homelith/pico_sign_sipf_xmodem/pcb/breadboard/breadboard.kicad_sch

## KiCad design pcb/breadboard/breadboard.kicad_sch (2022-04-09)

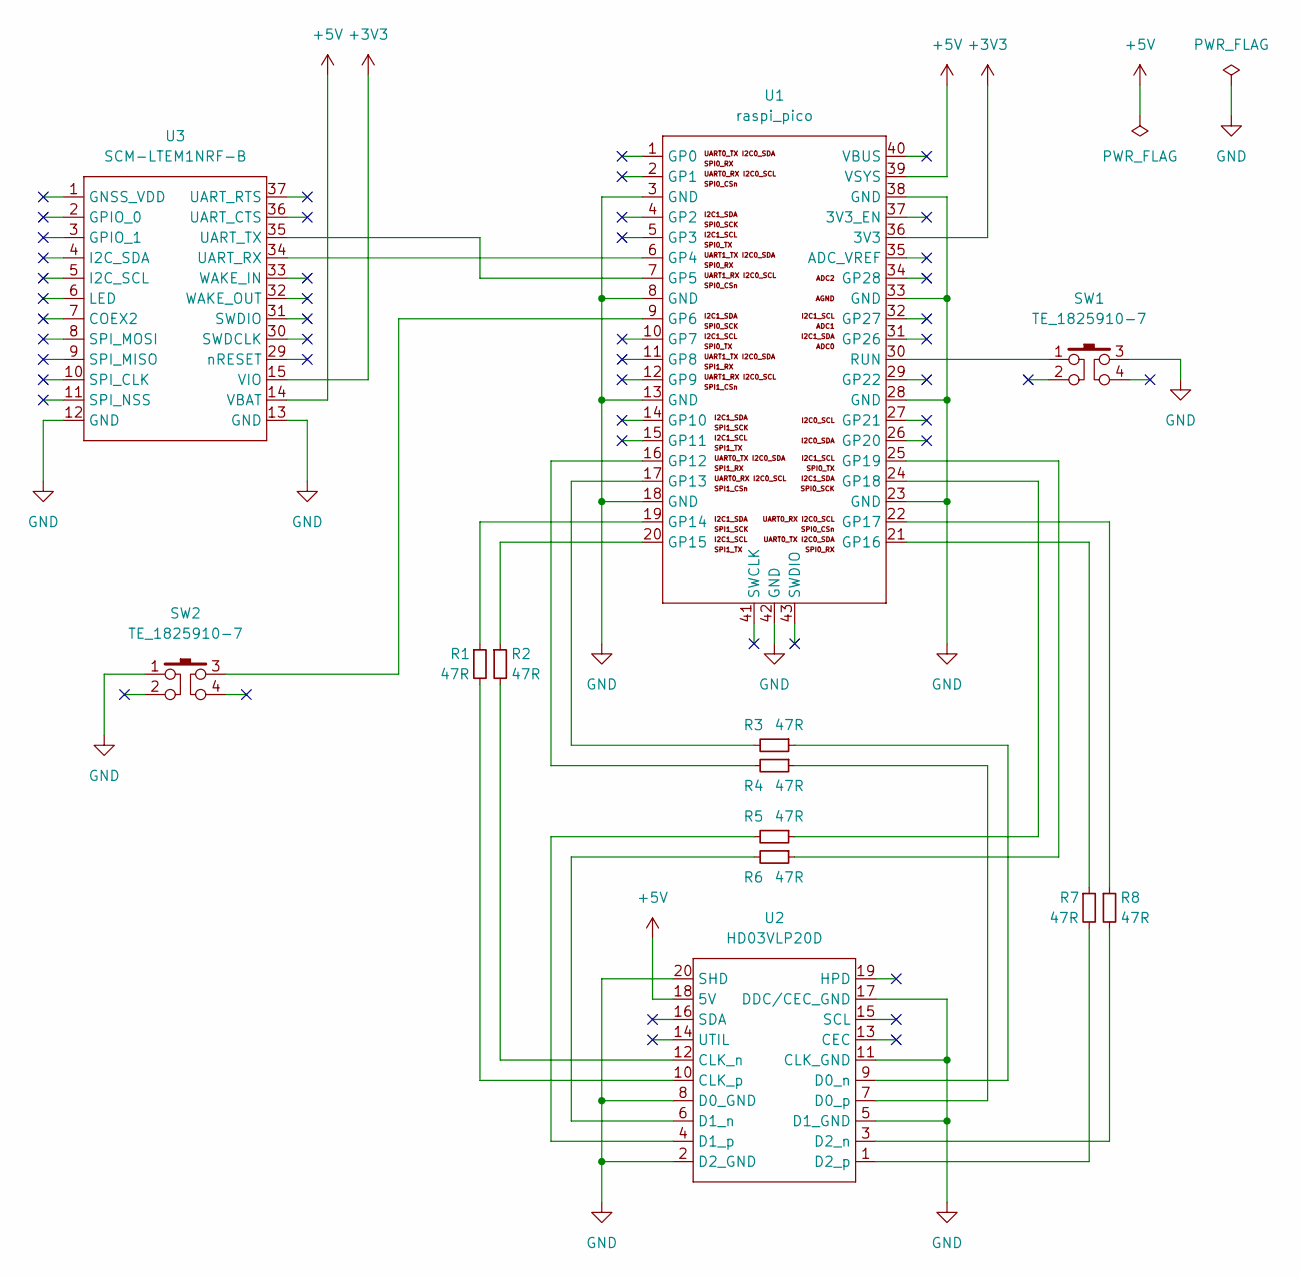
[picture p6: schematic breadboard.kicad_sch]

Parts:
R1, R2, R3, R4, R5, R6, R7, R8: 47R
SW1, SW2: TE_1825910-7
U1: raspi_pico
U2: HD03VLP20D
U3: SCM-LTEM1NRF-B

Connections:
+3V3: U1.36 (3V3), U3.15 (VIO)
+5V: U1.39 (VSYS), U2.18 (5V), U3.14 (VBAT)
GND: SW1.3, SW2.1, U1.3 (GND), U1.8 (GND), U1.13 (GND), U1.18 (GND), U1.23 (GND), U1.28 (GND), U1.33 (GND), U1.38 (GND), U1.42 (GND), U2.2 (D2_GND), U2.5 (D1_GND), U2.8 (D0_GND), U2.11 (CLK_GND), U2.17 (DDC/CEC_GND), U2.20 (SHD), U3.12 (GND), U3.13 (GND)
unnamed: R1.1, U1.19 (GP14)
unnamed: R1.2, U2.10 (CLK_p)
unnamed: R2.1, U1.20 (GP15)
unnamed: R2.2, U2.12 (CLK_n)
unnamed: R3.1, U2.9 (D0_n)
unnamed: R3.2, U1.17 (GP13)
unnamed: R4.1, U2.7 (D0_p)
unnamed: R4.2, U1.16 (GP12)
unnamed: R5.1, U1.24 (GP18)
unnamed: R5.2, U2.4 (D1_p)
unnamed: R6.1, U1.25 (GP19)
unnamed: R6.2, U2.6 (D1_n)
unnamed: R7.1, U1.21 (GP16)
unnamed: R7.2, U2.1 (D2_p)
unnamed: R8.1, U1.22 (GP17)
unnamed: R8.2, U2.3 (D2_n)
unnamed: SW1.1, U1.30 (RUN)
unnamed: SW2.3, U1.9 (GP6)
unnamed: U1.6 (GP4), U3.34 (UART_RX)
unnamed: U1.7 (GP5), U3.35 (UART_TX)
